yonaguska/QtPy_ESP32-S2/backend/grafana.png

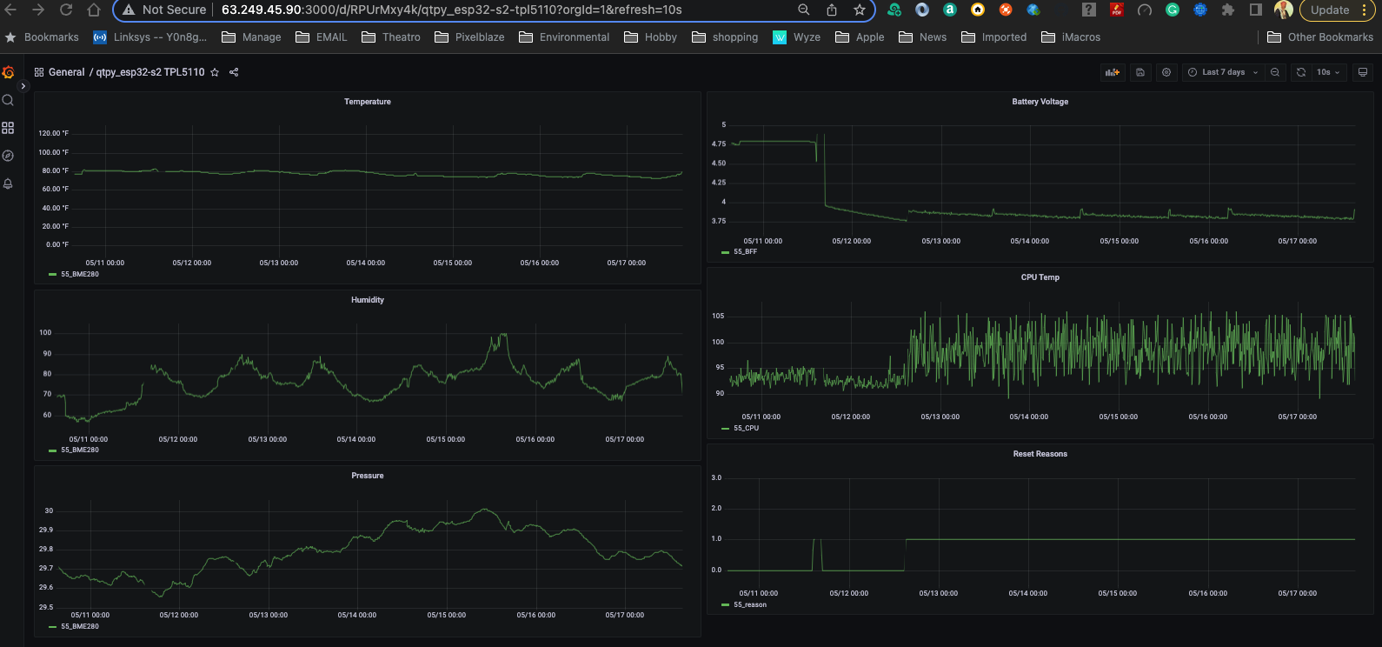
backend/grafana.png
