yonaguska/QtPy_ESP32-S2/backend/RP400_containers.png

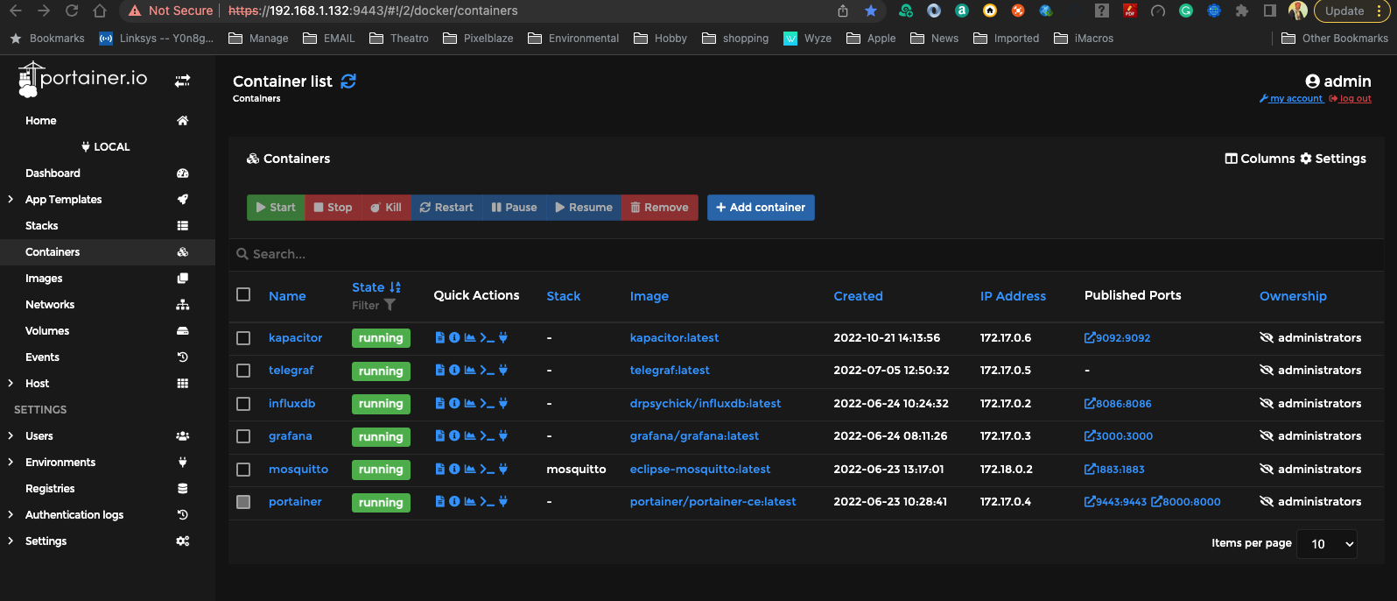
backend/RP400_containers.png
