yonaguska/QtPy_ESP32-S2/fritzing_files/QtPy-ESP32S2_bb.png

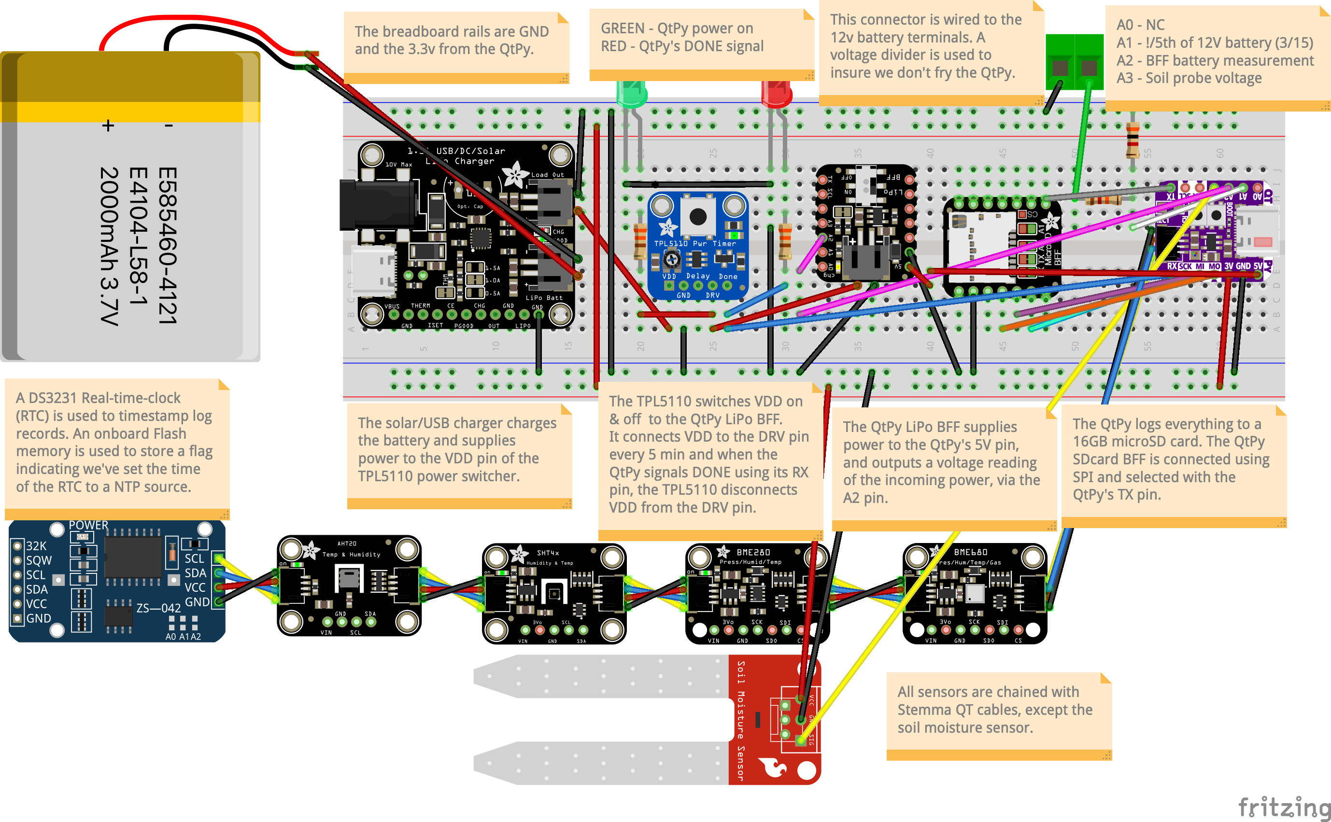
fritzing_files/QtPy-ESP32S2_bb.png
