yonaguska/QtPy_ESP32-S2/images/circuit_front.png

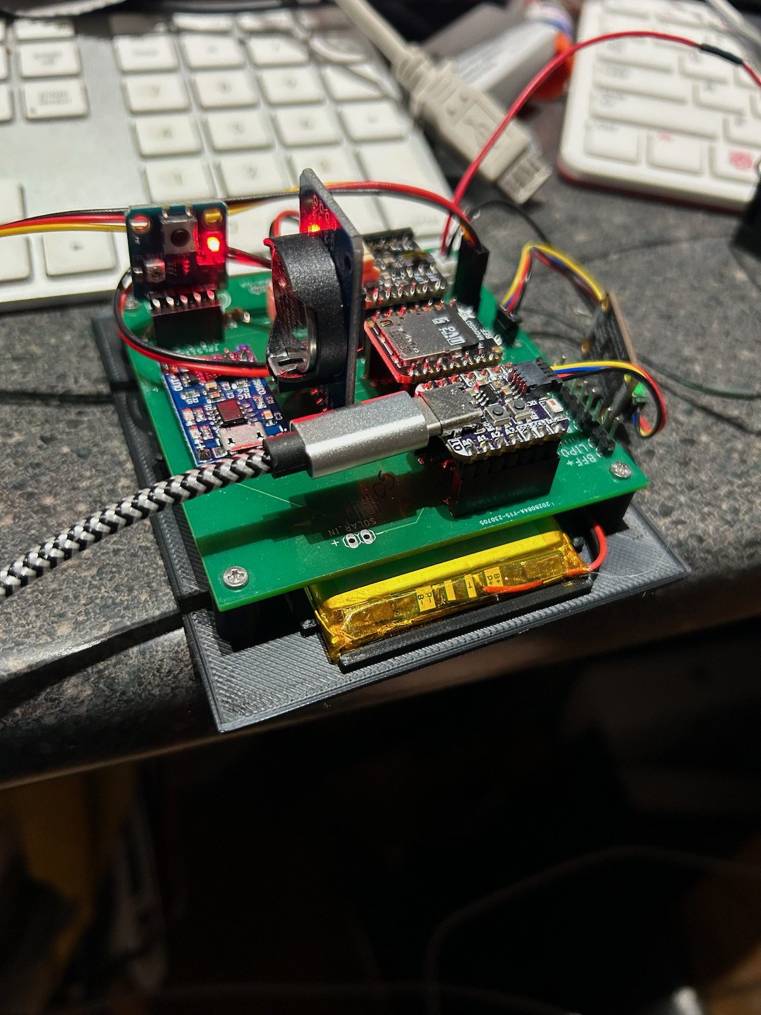
images/circuit_front.png
