yonaguska/QtPy_ESP32-S2/printables/circuit_on_base.png

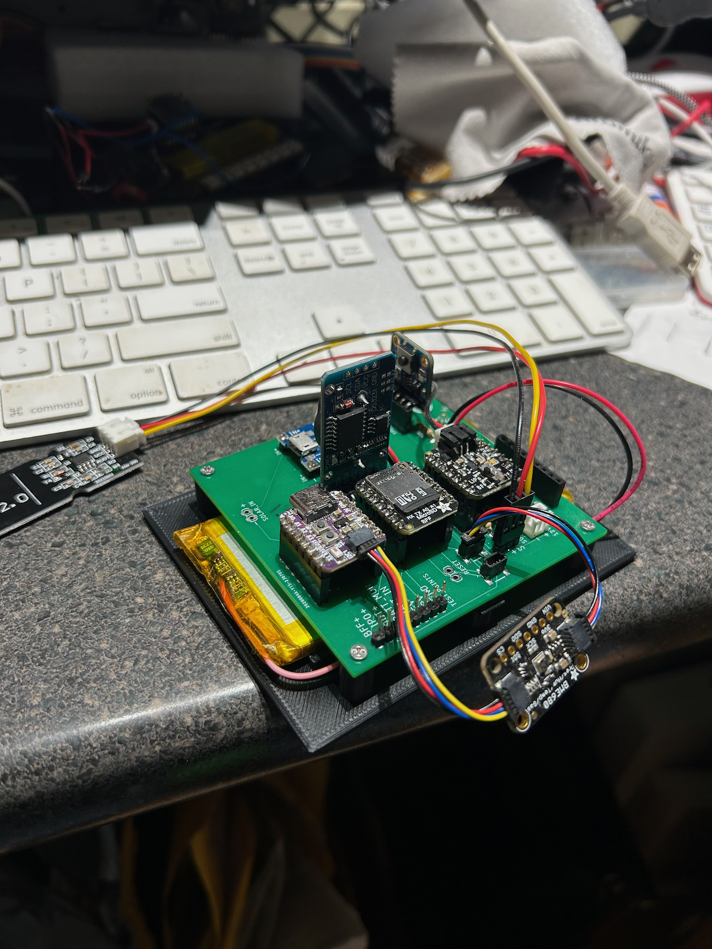
printables/circuit_on_base.png
