yonaguska/QtPy_ESP32-S2/leak_detector_scripts/a_secrets_file.py

# This file is where you keep secret settings, passwords, and tokens!
# If you put them in the code you risk committing that info or sharing it

secrets = {
    'ssid' : ’YOUR_WIFI_SSID’,
    'password' : ‘YOUR_SSID_PASSWORD’,

    # 'broker' : 'io.adafruit.com',
    'port' : 1883,
    #'aio_username' : “YOUR_ADAFRUIT_IO_USERNAME”,
    #'aio_key' : ‘YOUR_ADAFRUIT_IO_KEY”,
    'location' : ‘CITY, STATE COUNTRY’,


    'broker' : ‘YOUR_MQTT_BROKER_IP’,
    #'user' : ‘YOUR_MQTT_USERNAME,
    #'pass' : ‘YOUR_MQTT_PASSWORD’,
}
